JoaoMDFerreira/FPGA-Granular-Synthesizer/vhdl_src/MIDI_NOTE_PARSER.vhd

library IEEE;
use IEEE.STD_LOGIC_1164.ALL;
use IEEE.NUMERIC_STD.ALL;


entity MIDI_NOTE_PARSER is
    Port ( MIDI_NOTE : in  STD_LOGIC_VECTOR (6 downto 0);
           FREQUENCY : out  STD_LOGIC_VECTOR (35 downto 0));
end MIDI_NOTE_PARSER;

architecture Behavioral of MIDI_NOTE_PARSER is

begin
	FREQUENCY <=     std_logic_vector( to_unsigned(5618,36) ) when MIDI_NOTE = "0000000" else
                     std_logic_vector( to_unsigned(5952,36) ) when MIDI_NOTE = "0000001" else
                     std_logic_vector( to_unsigned(6306,36) ) when MIDI_NOTE = "0000010" else
                     std_logic_vector( to_unsigned(6681,36) ) when MIDI_NOTE = "0000011" else
                     std_logic_vector( to_unsigned(7079,36) ) when MIDI_NOTE = "0000100" else
                     std_logic_vector( to_unsigned(7500,36) ) when MIDI_NOTE = "0000101" else
                     std_logic_vector( to_unsigned(7946,36) ) when MIDI_NOTE = "0000110" else
                     std_logic_vector( to_unsigned(8418,36) ) when MIDI_NOTE = "0000111" else
                     std_logic_vector( to_unsigned(8919,36) ) when MIDI_NOTE = "0001000" else
                     std_logic_vector( to_unsigned(9449,36) ) when MIDI_NOTE = "0001001" else
                     std_logic_vector( to_unsigned(10011,36) ) when MIDI_NOTE = "0001010" else
                     std_logic_vector( to_unsigned(10606,36) ) when MIDI_NOTE = "0001011" else
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
                     std_logic_vector( to_unsigned(855219,36) ) when MIDI_NOTE = "1010111" else
                     std_logic_vector( to_unsigned(906073,36) ) when MIDI_NOTE = "1011000" else
                     std_logic_vector( to_unsigned(959951,36) ) when MIDI_NOTE = "1011001" else
                     std_logic_vector( to_unsigned(1017033,36) ) when MIDI_NOTE = "1011010" else
                     std_logic_vector( to_unsigned(1077509,36) ) when MIDI_NOTE = "1011011" else
                     std_logic_vector( to_unsigned(1141581,36) ) when MIDI_NOTE = "1011100" else
                     std_logic_vector( to_unsigned(1209463,36) ) when MIDI_NOTE = "1011101" else
                     std_logic_vector( to_unsigned(1281381,36) ) when MIDI_NOTE = "1011110" else
                     std_logic_vector( to_unsigned(1357576,36) ) when MIDI_NOTE = "1011111" else
                     std_logic_vector( to_unsigned(1438302,36) ) when MIDI_NOTE = "1100000" else
                     std_logic_vector( to_unsigned(1523828,36) ) when MIDI_NOTE = "1100001" else
                     std_logic_vector( to_unsigned(1614439,36) ) when MIDI_NOTE = "1100010" else
                     std_logic_vector( to_unsigned(1710439,36) ) when MIDI_NOTE = "1100011" else
                     std_logic_vector( to_unsigned(1812147,36) ) when MIDI_NOTE = "1100100" else
                     std_logic_vector( to_unsigned(1919903,36) ) when MIDI_NOTE = "1100101" else
                     std_logic_vector( to_unsigned(2034066,36) ) when MIDI_NOTE = "1100110" else
                     std_logic_vector( to_unsigned(2155018,36) ) when MIDI_NOTE = "1100111" else
                     std_logic_vector( to_unsigned(2283162,36) ) when MIDI_NOTE = "1101000" else
                     std_logic_vector( to_unsigned(2418926,36) ) when MIDI_NOTE = "1101001" else
                     std_logic_vector( to_unsigned(2562762,36) ) when MIDI_NOTE = "1101010" else
                     std_logic_vector( to_unsigned(2715152,36) ) when MIDI_NOTE = "1101011" else
                     std_logic_vector( to_unsigned(2876604,36) ) when MIDI_NOTE = "1101100" else
                     std_logic_vector( to_unsigned(3047655,36) ) when MIDI_NOTE = "1101101" else
                     std_logic_vector( to_unsigned(3228878,36) ) when MIDI_NOTE = "1101110" else
                     std_logic_vector( to_unsigned(3420877,36) ) when MIDI_NOTE = "1101111" else
                     std_logic_vector( to_unsigned(3624293,36) ) when MIDI_NOTE = "1110000" else
                     std_logic_vector( to_unsigned(3839805,36) ) when MIDI_NOTE = "1110001" else
                     std_logic_vector( to_unsigned(4068132,36) ) when MIDI_NOTE = "1110010" else
                     std_logic_vector( to_unsigned(4310035,36) ) when MIDI_NOTE = "1110011" else
                     std_logic_vector( to_unsigned(4566323,36) ) when MIDI_NOTE = "1110100" else
                     std_logic_vector( to_unsigned(4837851,36) ) when MIDI_NOTE = "1110101" else
                     std_logic_vector( to_unsigned(5125525,36) ) when MIDI_NOTE = "1110110" else
                     std_logic_vector( to_unsigned(5430304,36) ) when MIDI_NOTE = "1110111" else
                     std_logic_vector( to_unsigned(5753207,36) ) when MIDI_NOTE = "1111000" else
                     std_logic_vector( to_unsigned(6095311,36) ) when MIDI_NOTE = "1111001" else
                     std_logic_vector( to_unsigned(6457757,36) ) when MIDI_NOTE = "1111010" else
                     std_logic_vector( to_unsigned(6841755,36) ) when MIDI_NOTE = "1111011" else
                     std_logic_vector( to_unsigned(7248587,36) ) when MIDI_NOTE = "1111100" else
                     std_logic_vector( to_unsigned(7679610,36) ) when MIDI_NOTE = "1111101" else
                     std_logic_vector( to_unsigned(8136263,36) ) when MIDI_NOTE = "1111110" else
                     std_logic_vector( to_unsigned(8620071,36) ) when MIDI_NOTE = "1111111" else
					 (others => '0');
	
end Behavioral;
